robots/stm32-ticc/main/platform.h

#ifndef PLATFORM_H_
#define PLATFORM_H_

#include <stdint.h>
#include <string.h>
#include "stm32f0xx.h"

#define LIKELY(x)          __builtin_expect(!!(x), 1)
#define UNLIKELY(x)        __builtin_expect(!!(x), 0)
#define ARRAY_SIZE(x)      ((sizeof(x)/sizeof(x[0])))
#define BV(x)              (1 << (x))
#define ABS(x)             (((x)>0)?(x):(-(x)))
#define MAX(x,y)           ((x)>(y)?(x):(y))
#ifndef MIN
#define MIN(x,y)           ((x)>(y)?(y):(x))
#endif

#define PACK               __attribute__ ((packed))

#define ASSERT_CONCAT_(a, b) a##b
#define ASSERT_CONCAT(a, b) ASSERT_CONCAT_(a, b)

/* These can't be used after statements in c89. */
#ifdef __COUNTER__
	#define STATIC_ASSERT(e,m) \
		{ enum { ASSERT_CONCAT(static_assert_, __COUNTER__) = 1/(!!(e)) }; }
#else
	/* This can't be used twice on the same line so ensure if using in headers
	 * that the headers are not included twice (by wrapping in #ifndef...#endif)
	 * Note it doesn't cause an issue when used on same line of separate modules
	 * compiled with gcc -combine -fwhole-program.  */
	#define STATIC_ASSERT(e,m) \
		{ enum { ASSERT_CONCAT(assert_line_, __LINE__) = 1/(!!(e)) }; }
#endif

#define MAGIC_KEY  0xDEADBEEF

#endif
